ahmadmadyy/Coordinate-Tracking-Car/Hardware Design/1.png

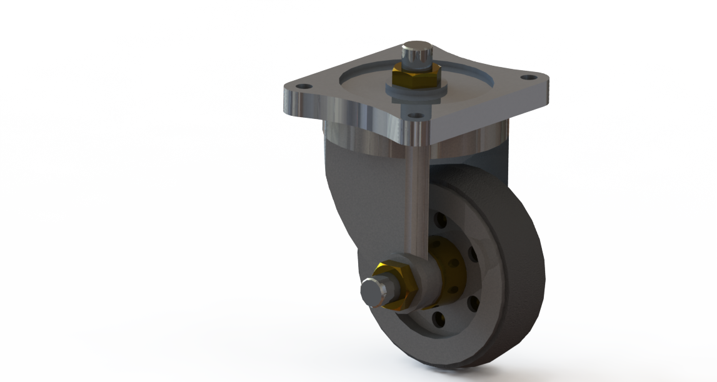
Hardware Design/1.png
