ahmadmadyy/Coordinate-Tracking-Car/Hardware Design/2021-05-19 (1).png

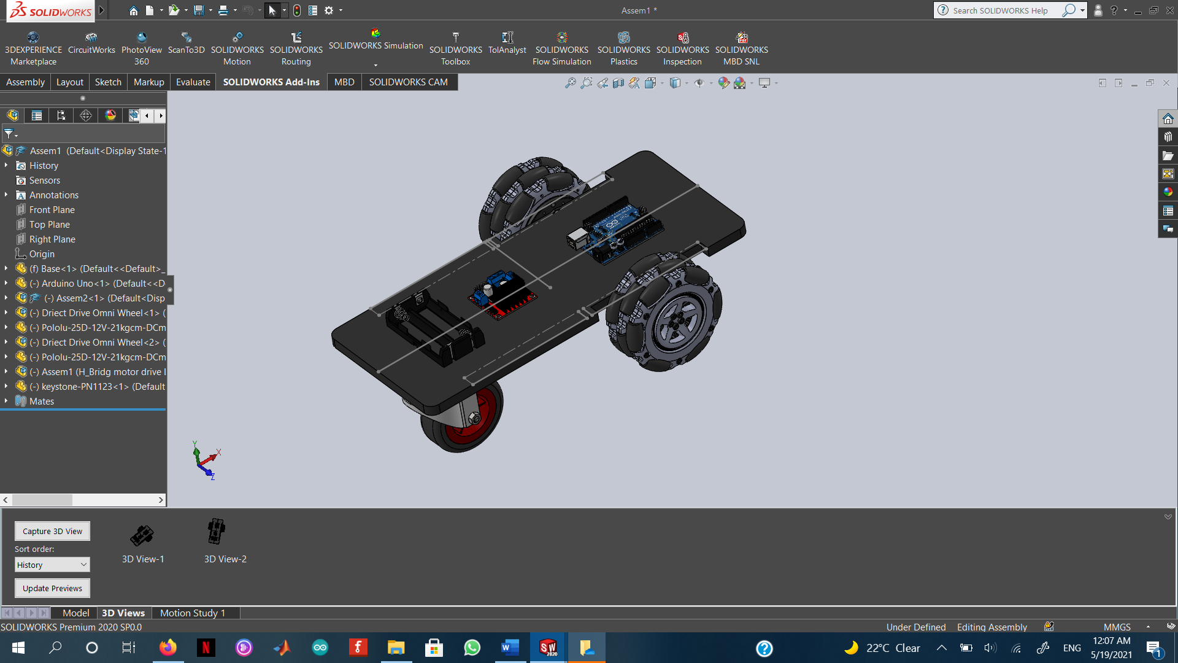
Hardware Design/2021-05-19 (1).png
