ahmadmadyy/Coordinate-Tracking-Car/Hardware Design/2021-05-19 (2).png

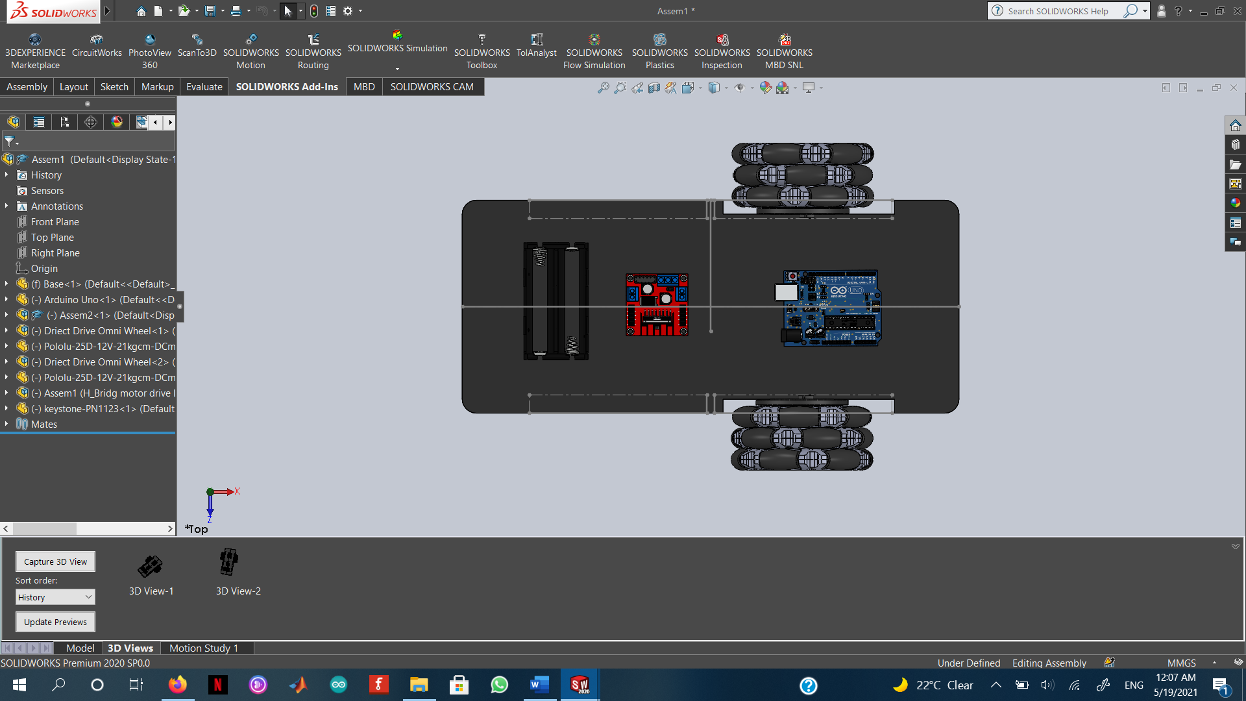
Hardware Design/2021-05-19 (2).png
