ahmadmadyy/Coordinate-Tracking-Car/Hardware Design/2021-05-19 (3).png

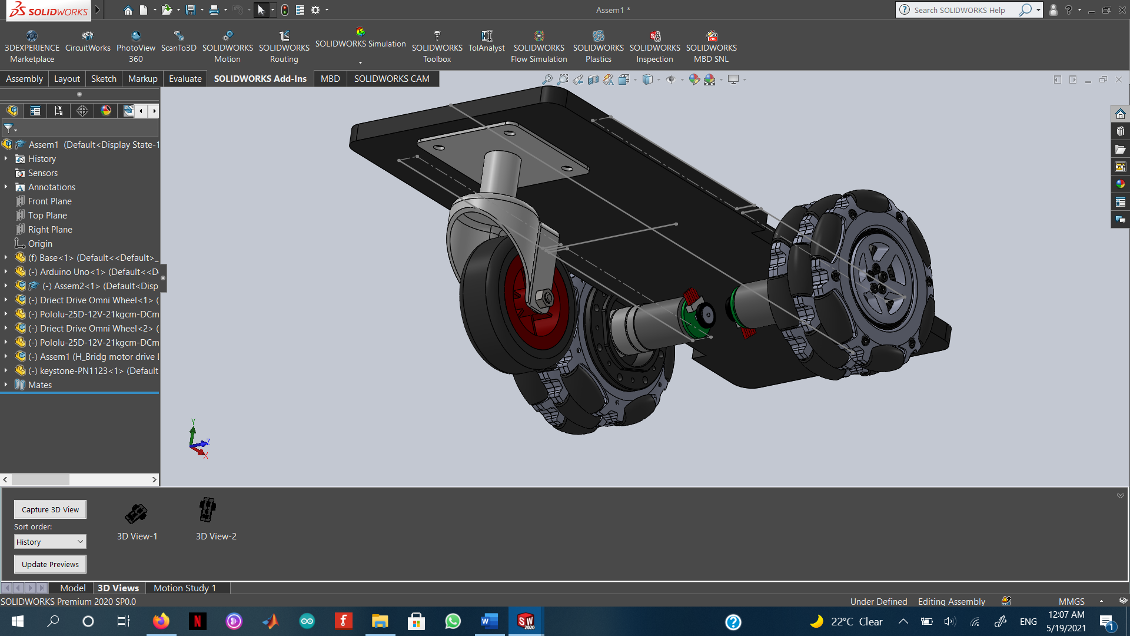
Hardware Design/2021-05-19 (3).png
