ahmadmadyy/Coordinate-Tracking-Car/Hardware Design/Capture2.PNG

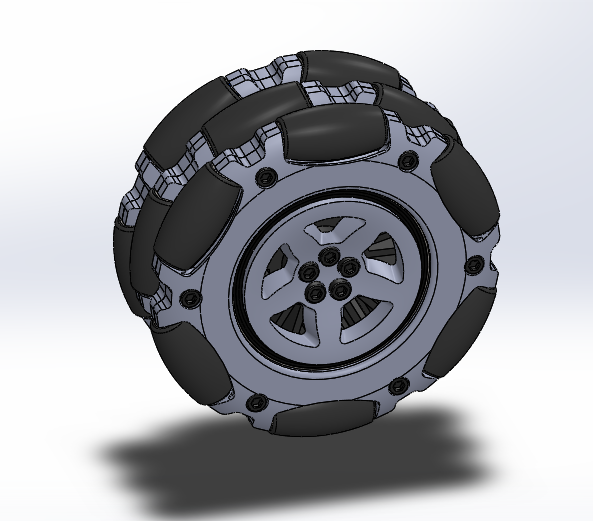
Hardware Design/Capture2.PNG
