ahmadmadyy/Coordinate-Tracking-Car/Hardware Design/Capture3.PNG

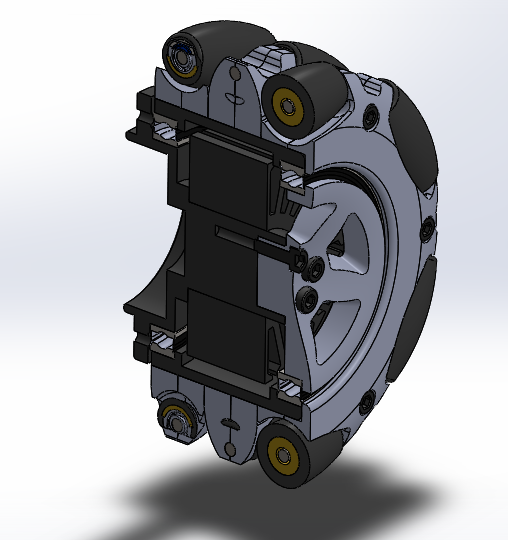
Hardware Design/Capture3.PNG
