ahmadmadyy/Coordinate-Tracking-Car/Hardware Design/Capture.JPG

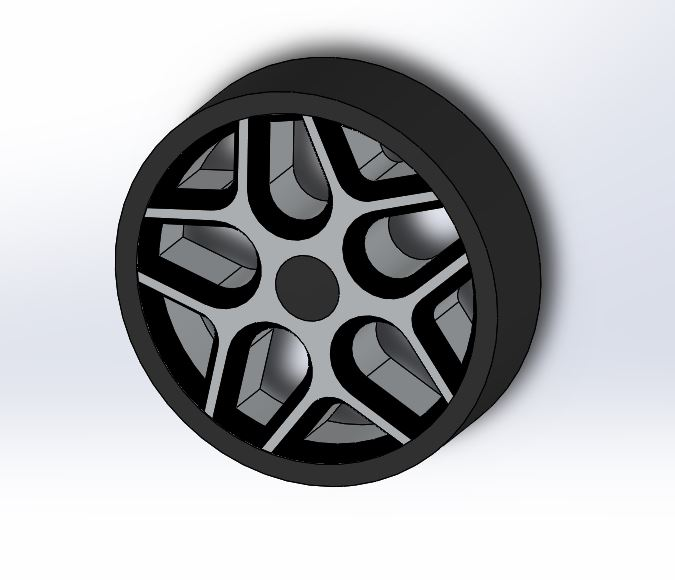
Hardware Design/Capture.JPG
