ahmadmadyy/Coordinate-Tracking-Car/Hardware Design/Capture.PNG

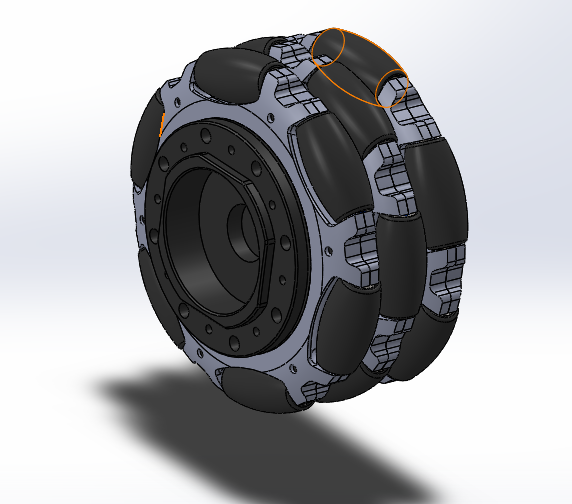
Hardware Design/Capture.PNG
