ahmadmadyy/Coordinate-Tracking-Car/Hardware Design/Castor wheel.JPG

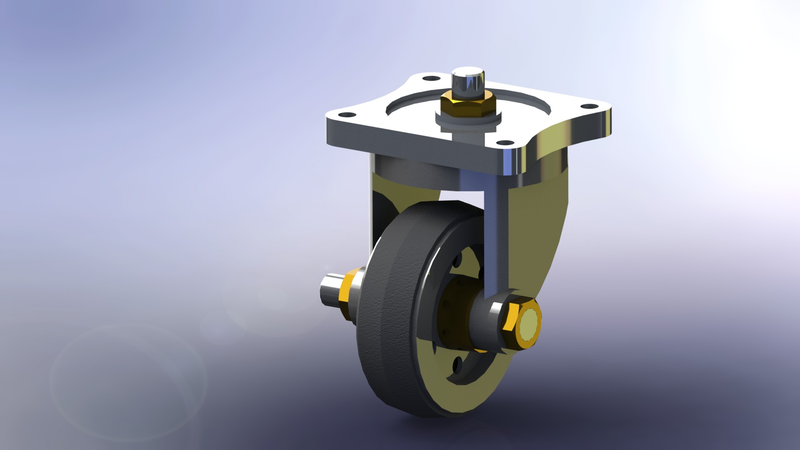
Hardware Design/Castor wheel.JPG
