ahmadmadyy/Coordinate-Tracking-Car/Hardware Design/h_bridg-motor-drive-l298n-1.snapshot.1/Assem final (H_Bridg)/Assem final (H_Bridg)/New folder/66.JPG

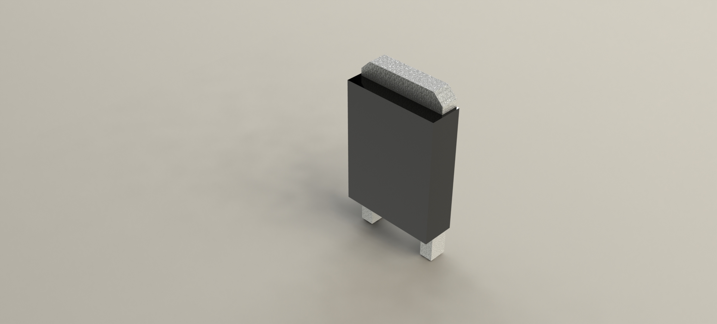
Hardware Design/h_bridg-motor-drive-l298n-1.snapshot.1/Assem final (H_Bridg)/Assem final (H_Bridg)/New folder/66.JPG
