ahmadmadyy/Coordinate-Tracking-Car/Hardware Design/keystone-PN1123 iso rendering 2.JPG

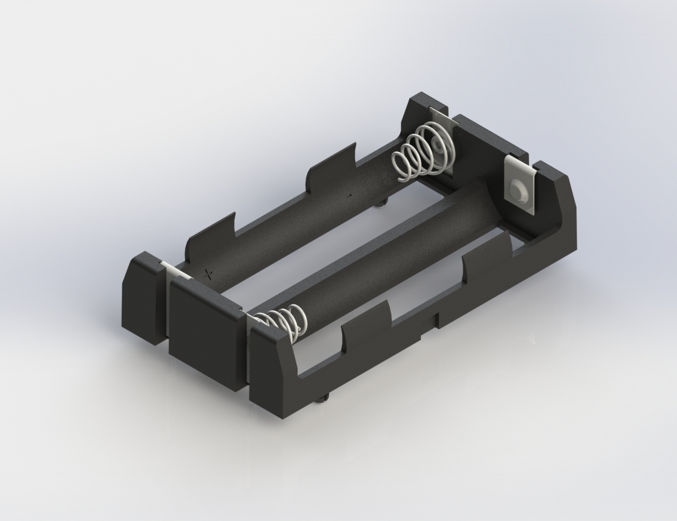
Hardware Design/keystone-PN1123 iso rendering 2.JPG
