ahmadmadyy/Coordinate-Tracking-Car/Hardware Design/keystone-PN1123 mechanical.JPG

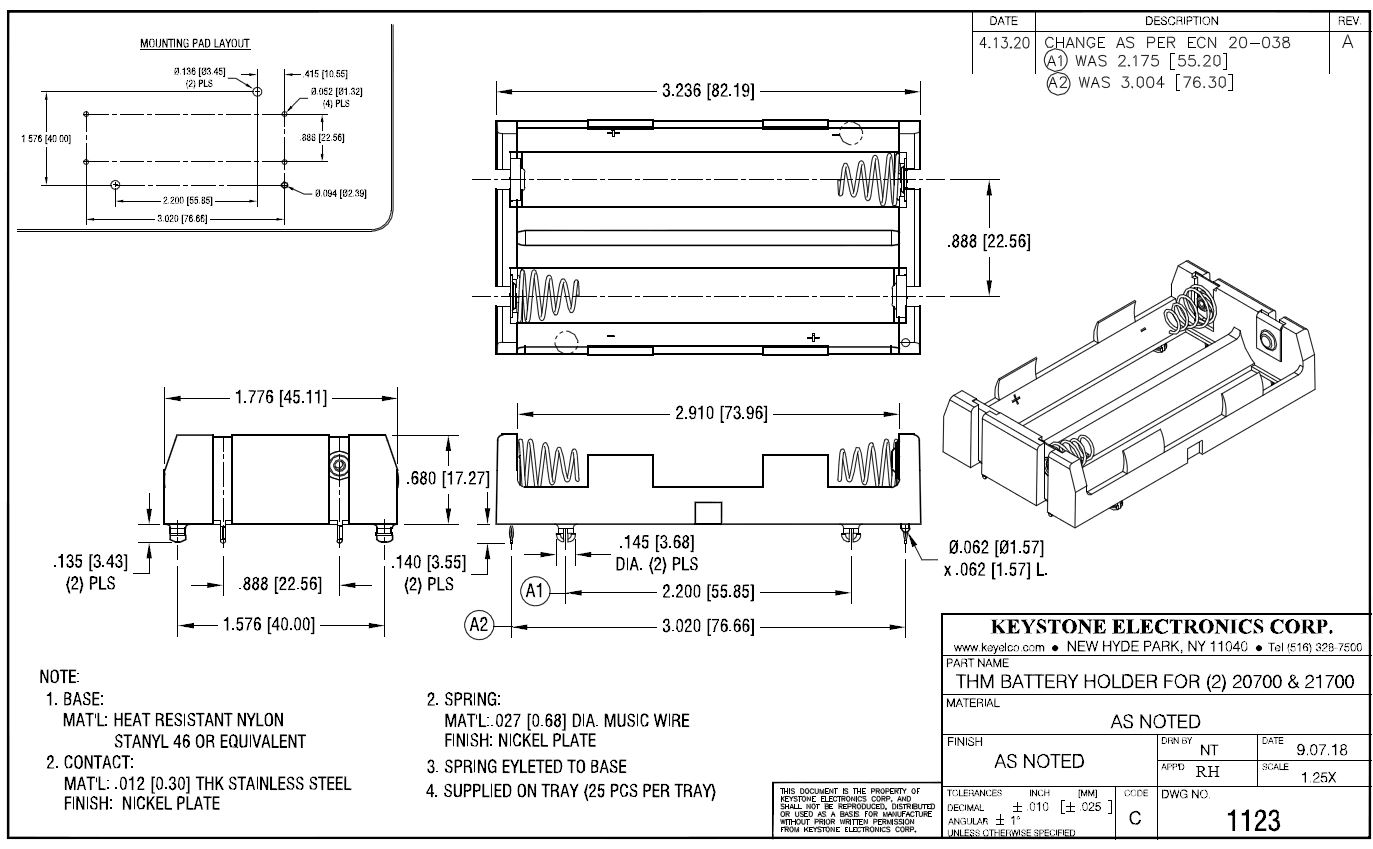
Hardware Design/keystone-PN1123 mechanical.JPG
