ahmadmadyy/Coordinate-Tracking-Car/Hardware Design/keystone-PN1123 photo.JPG

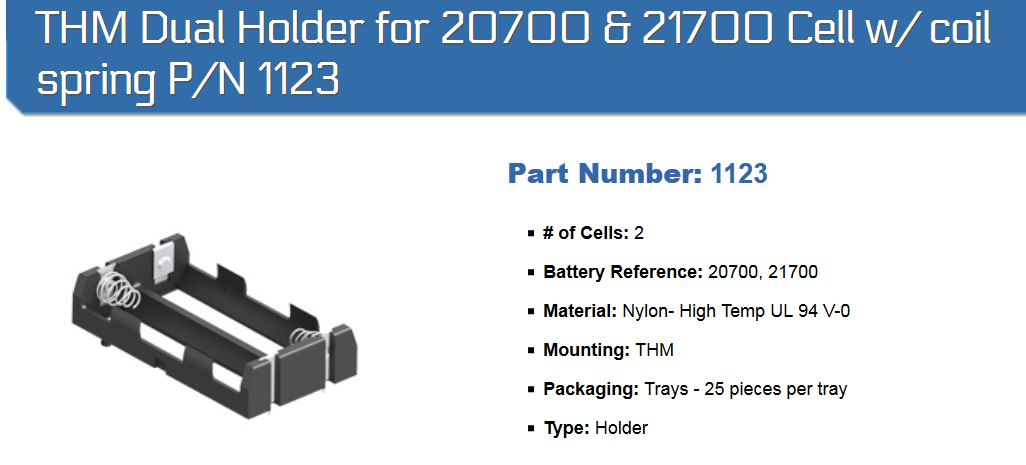
Hardware Design/keystone-PN1123 photo.JPG
