ahmadmadyy/Coordinate-Tracking-Car/Hardware Design/Renderings/untitled.642.jpg

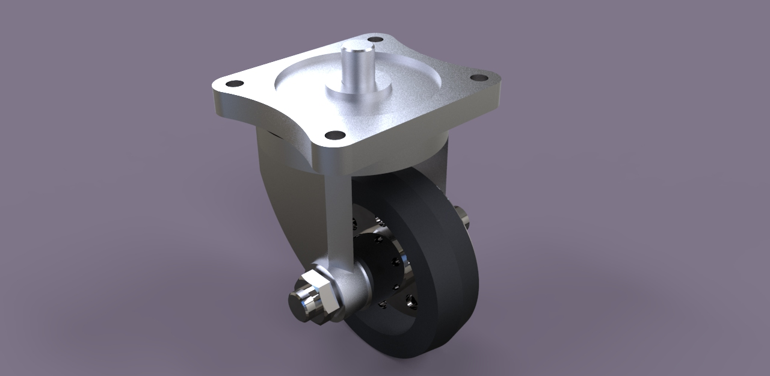
Hardware Design/Renderings/untitled.642.jpg
