ahmadmadyy/Coordinate-Tracking-Car/Hardware Design/View.JPG

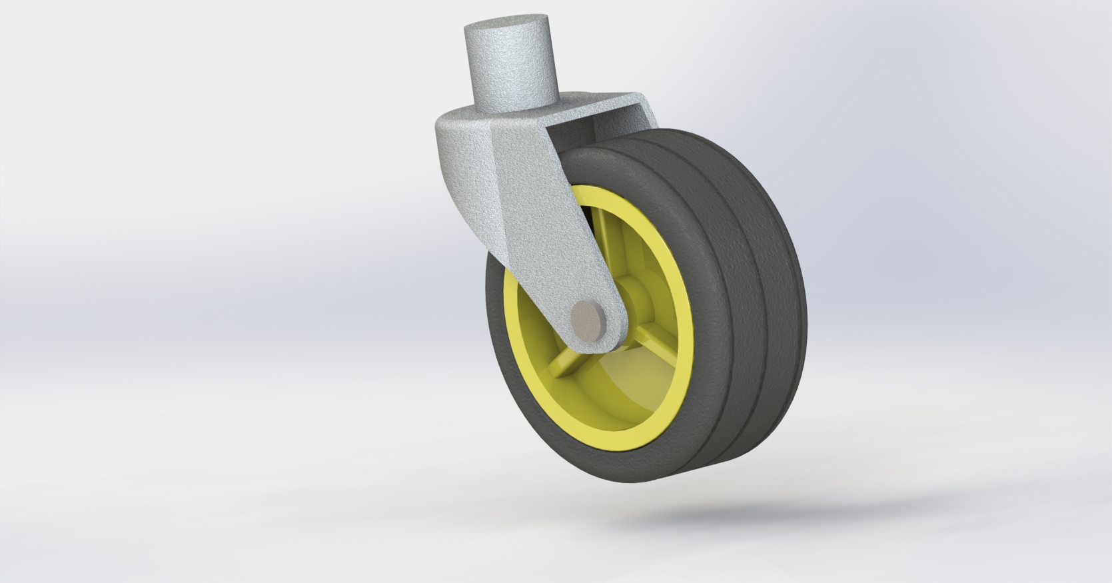
Hardware Design/View.JPG
