ahmadmadyy/Coordinate-Tracking-Car/Hardware Design/wheel/JPG/Assem2.JPG

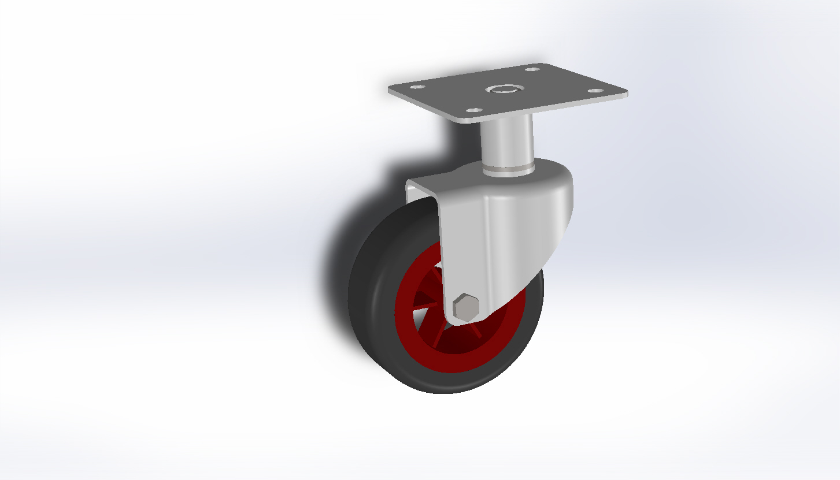
Hardware Design/wheel/JPG/Assem2.JPG
