ahmadmadyy/Coordinate-Tracking-Car/Hardware Design/wheel/JPG/Assem3.JPG

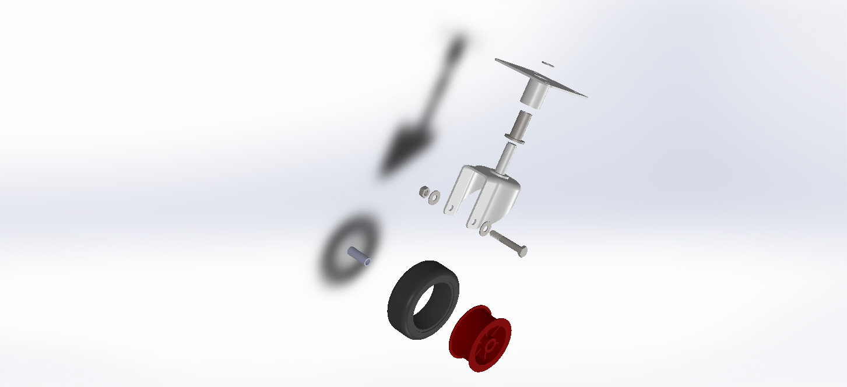
Hardware Design/wheel/JPG/Assem3.JPG
