ahmadmadyy/Coordinate-Tracking-Car/Hardware Design/wheel/JPG/Ring.JPG

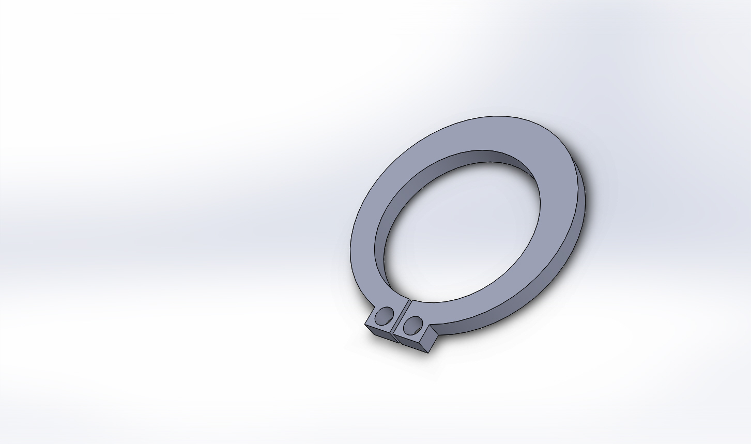
Hardware Design/wheel/JPG/Ring.JPG
