ahmadmadyy/Coordinate-Tracking-Car/Hardware Design/wheel/JPG/screw M6.JPG

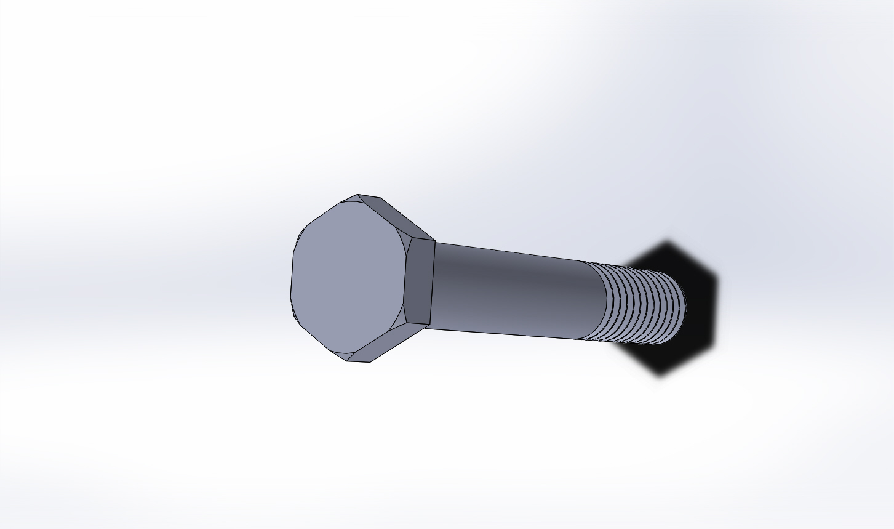
Hardware Design/wheel/JPG/screw M6.JPG
