ahmadmadyy/Coordinate-Tracking-Car/Hardware Design/wheel/JPG/screw nut m6.JPG

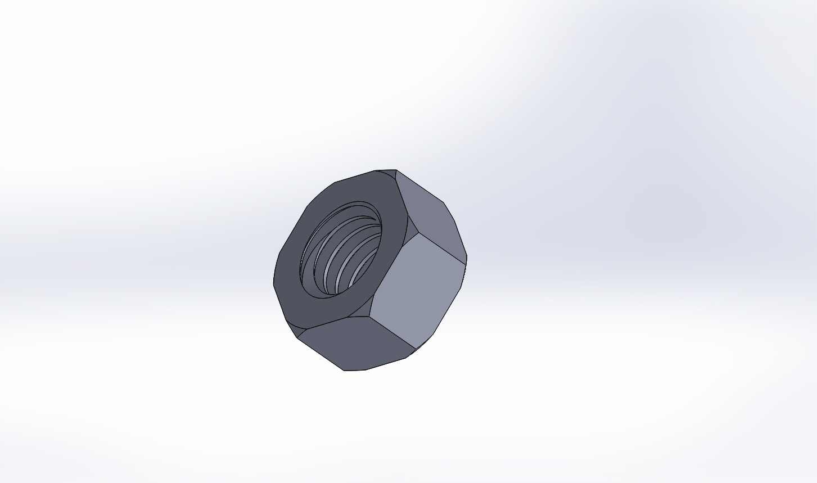
Hardware Design/wheel/JPG/screw nut m6.JPG
