ahmadmadyy/Coordinate-Tracking-Car/Hardware Design/wheel/JPG/Support plate .JPG

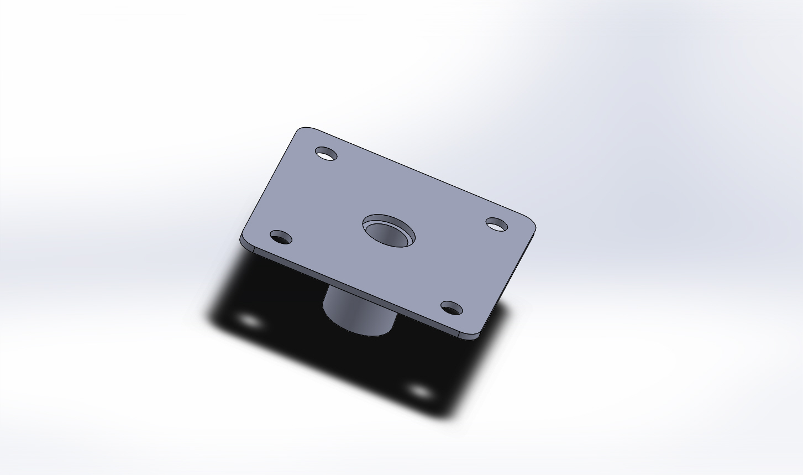
Hardware Design/wheel/JPG/Support plate .JPG
