ahmadmadyy/Coordinate-Tracking-Car/Hardware Design/wheel/JPG/tire.JPG

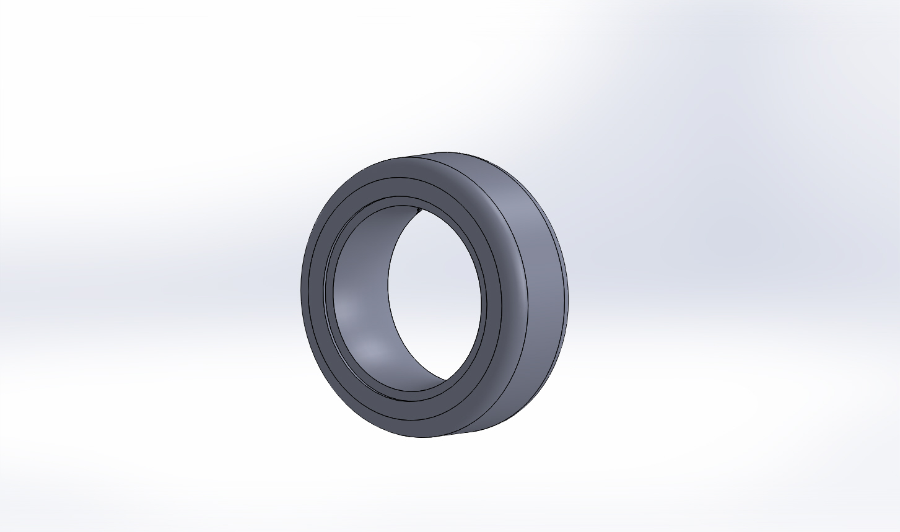
Hardware Design/wheel/JPG/tire.JPG
