ahmadmadyy/Coordinate-Tracking-Car/Hardware Design/wheel/JPG/wheel carrier.JPG

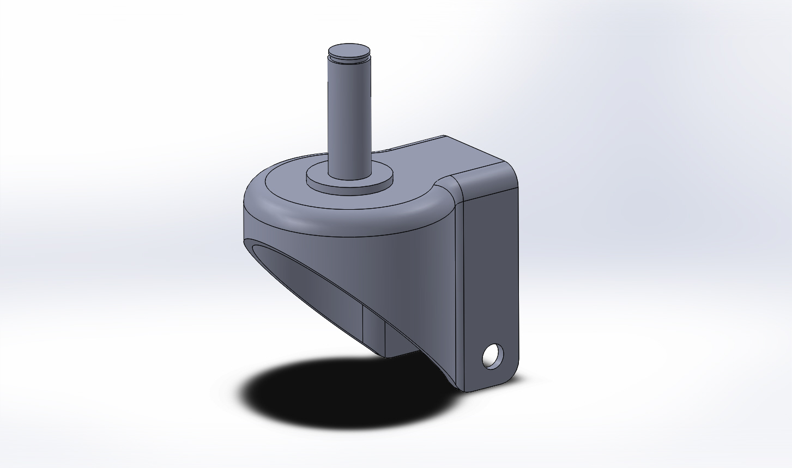
Hardware Design/wheel/JPG/wheel carrier.JPG
