ahmadmadyy/Coordinate-Tracking-Car/Hardware Design/wheel/JPG/wheel.JPG

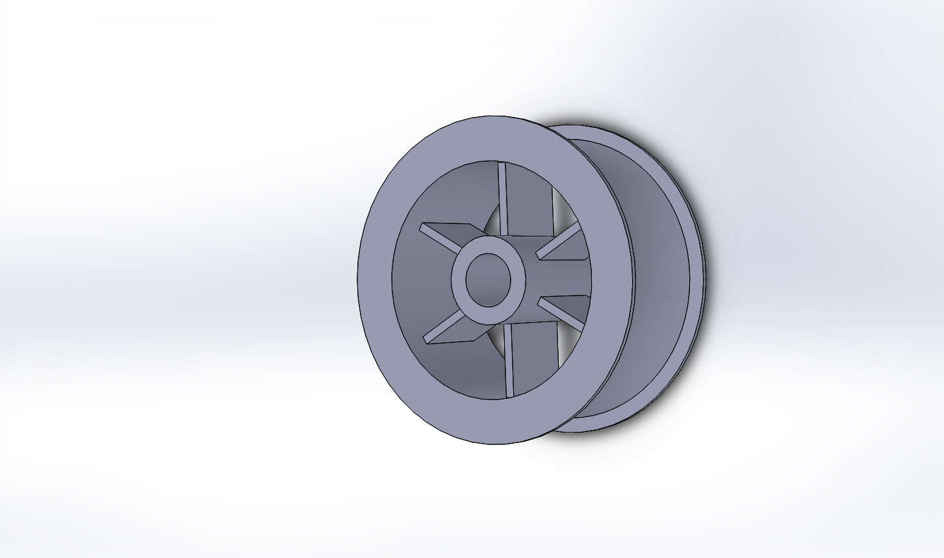
Hardware Design/wheel/JPG/wheel.JPG
