ahmadmadyy/Coordinate-Tracking-Car/Hardware Design/Поворотные колесо d200мм/render_1.jpg

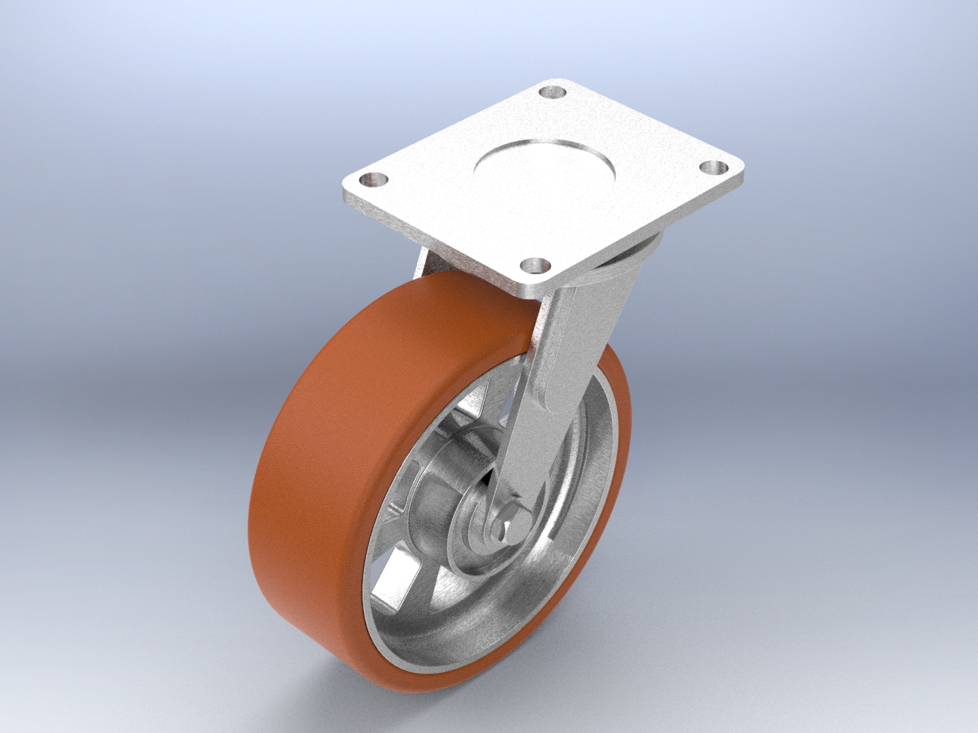
Hardware Design/Поворотные колесо d200мм/render_1.jpg
