ahmadmadyy/Coordinate-Tracking-Car/Hardware Design/Поворотные колесо d200мм/render_2.jpg

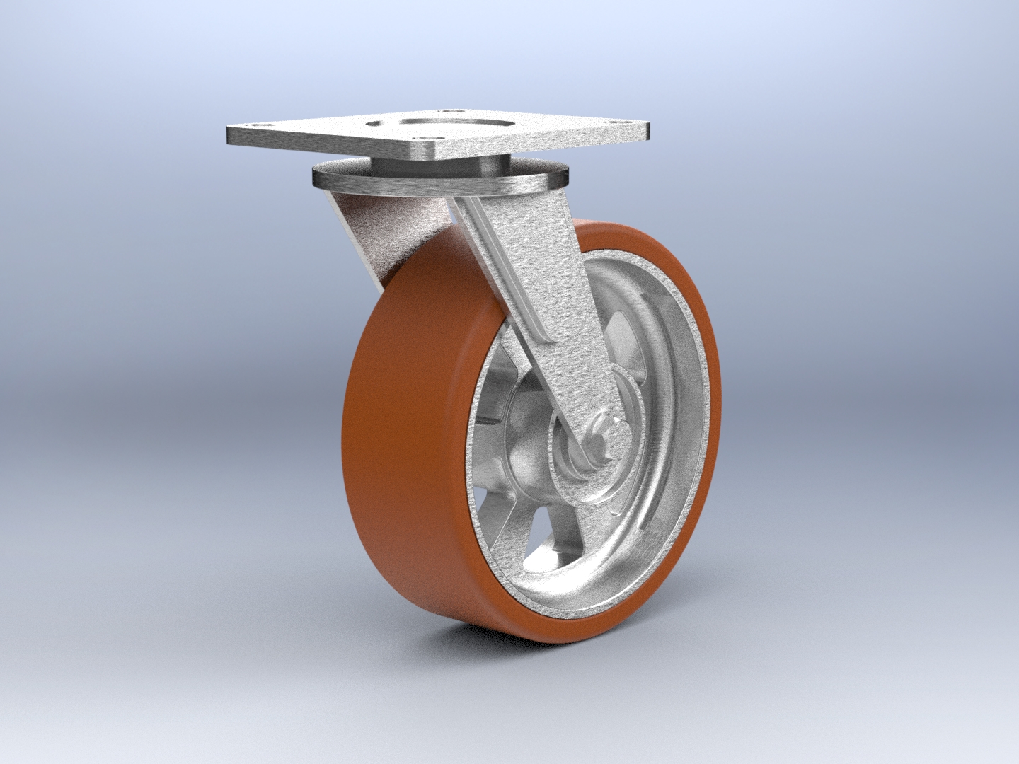
Hardware Design/Поворотные колесо d200мм/render_2.jpg
