ahmadmadyy/Coordinate-Tracking-Car/Hardware Design/Поворотные колесо d200мм/render_3.jpg

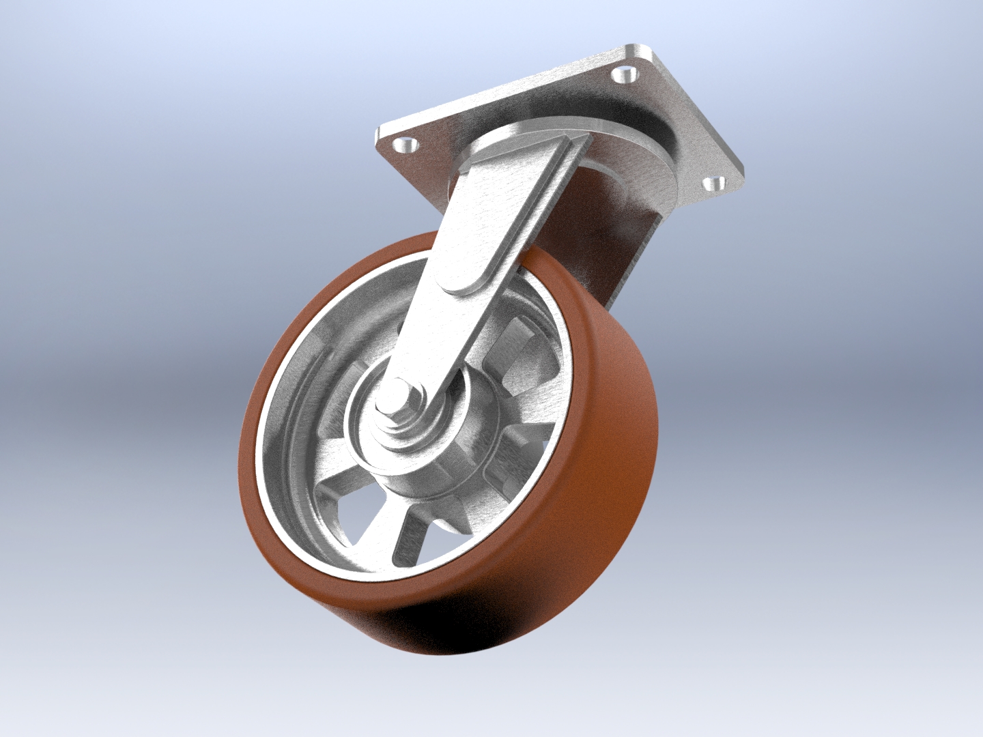
Hardware Design/Поворотные колесо d200мм/render_3.jpg
