ahmadmadyy/Coordinate-Tracking-Car/Media/20210617_170247.jpg

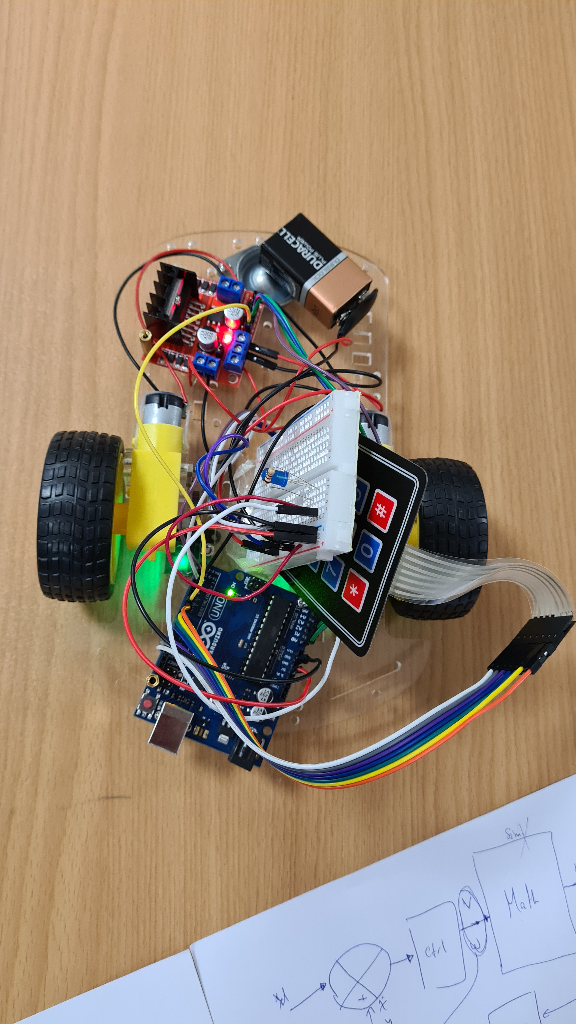
Media/20210617_170247.jpg
