ahmadmadyy/Coordinate-Tracking-Car/Media/20210617_170249.jpg

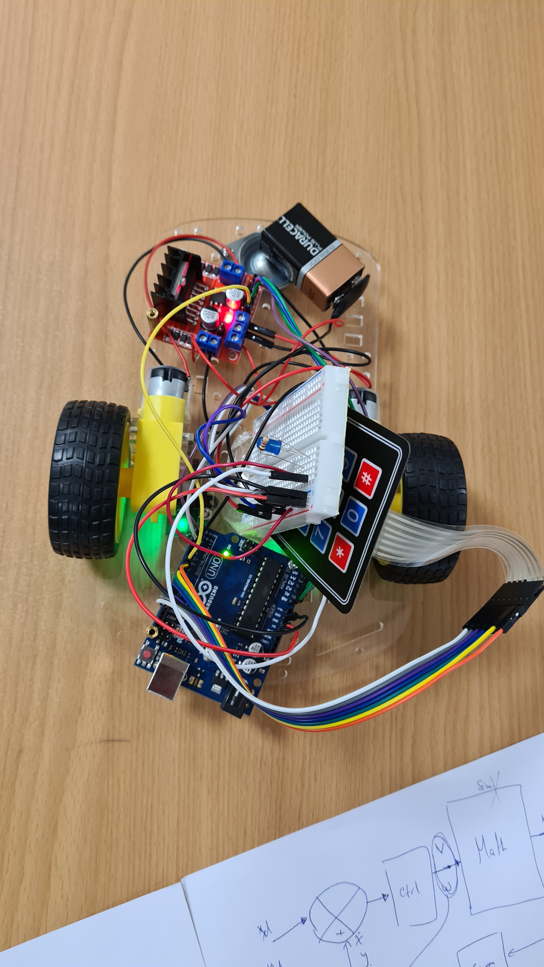
Media/20210617_170249.jpg
