ahmadmadyy/Coordinate-Tracking-Car/Media/20210622_192925.jpg

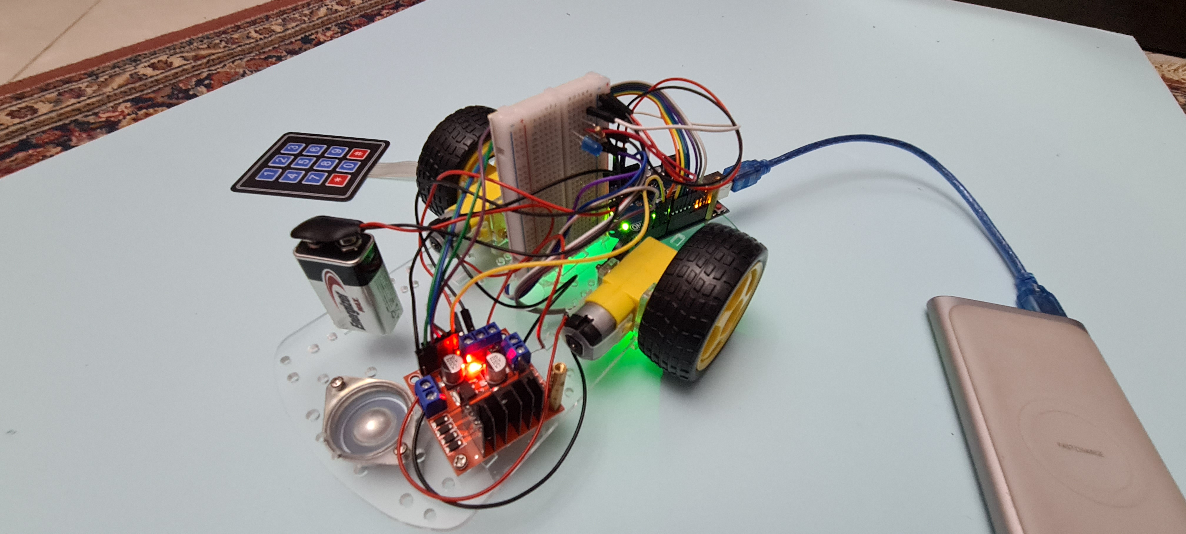
Media/20210622_192925.jpg
