ahmadmadyy/Coordinate-Tracking-Car/Media/20210622_192959.jpg

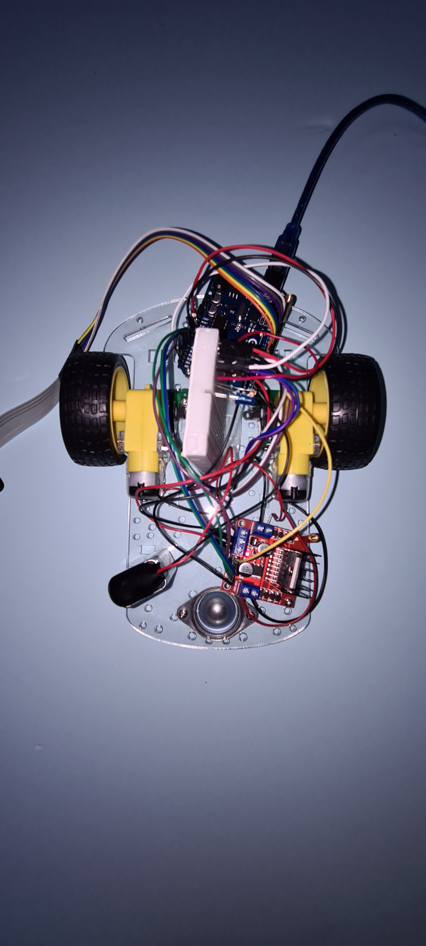
Media/20210622_192959.jpg
