ahmadmadyy/Coordinate-Tracking-Car/Media/20210622_193133.jpg

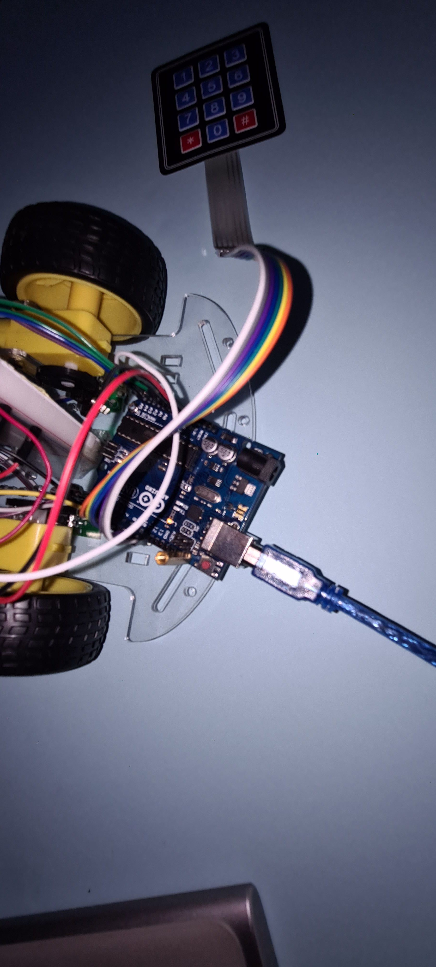
Media/20210622_193133.jpg
