ahmadmadyy/Coordinate-Tracking-Car/Media/20210622_193256.jpg

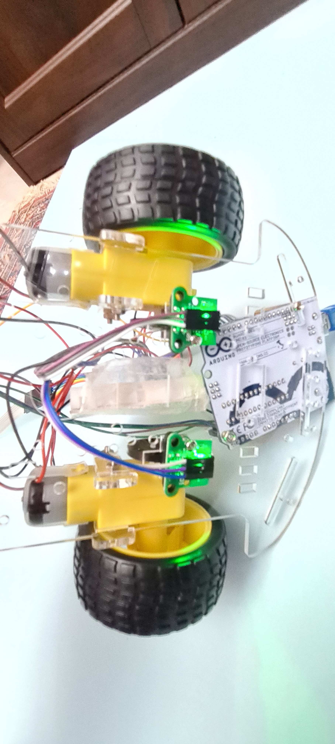
Media/20210622_193256.jpg
