ahmadmadyy/Coordinate-Tracking-Car/Media/20210622_193330.jpg

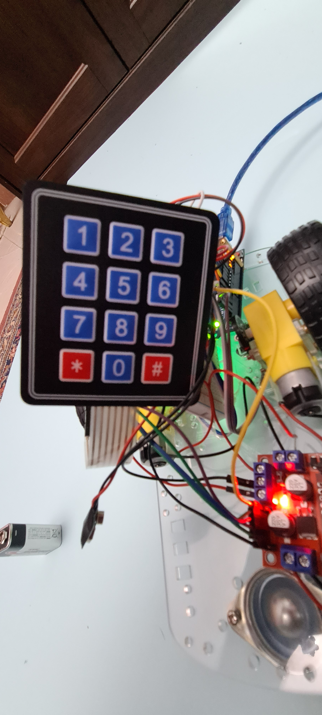
Media/20210622_193330.jpg
