ahmadmadyy/Coordinate-Tracking-Car/Hardware Design/h_bridg-motor-drive-l298n-1.snapshot.1/Assem final (H_Bridg)/Dual pin header.SLDPRT

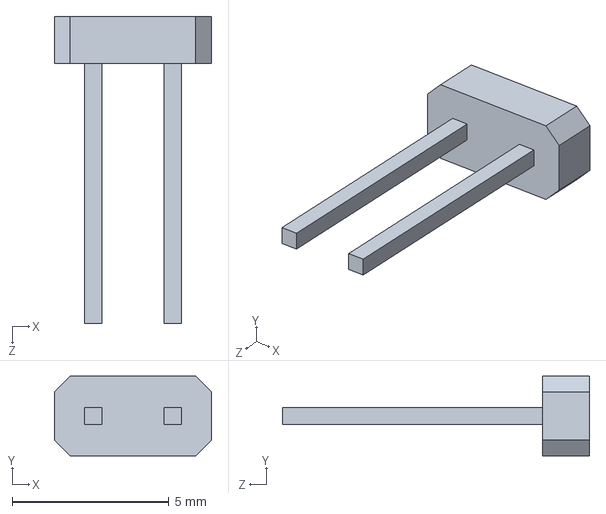
[picture p91: CAD file, 2023-09-04]
Hardware Design/h_bridg-motor-drive-l298n-1.snapshot.1/Assem final (H_Bridg)/Dual pin header.SLDPRT
5.00 x 2.54 x 9.80 mm
