ahmadmadyy/Coordinate-Tracking-Car/Hardware Design/wheel/Support plate .SLDPRT

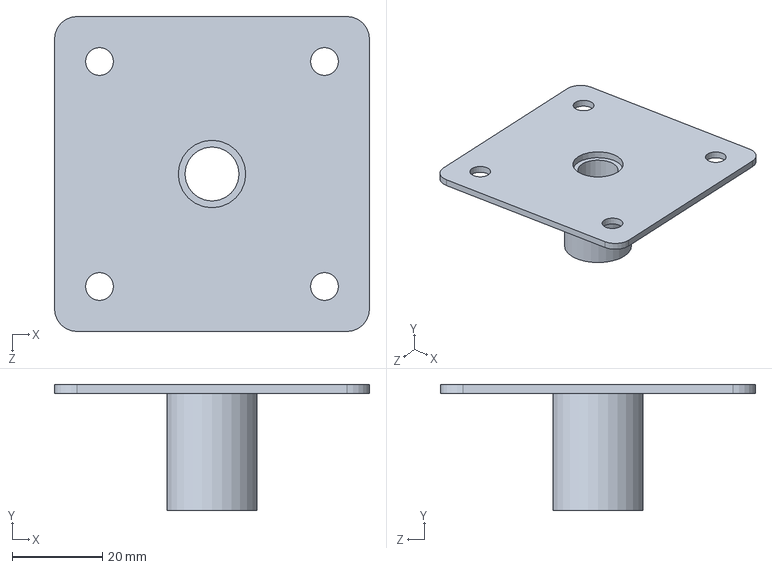
[picture p92: CAD file, 2023-09-04]
Hardware Design/wheel/Support plate .SLDPRT
70.0 x 28.0 x 70.0 mm
