ahmadmadyy/Coordinate-Tracking-Car/Hardware Design/h_bridg-motor-drive-l298n-1.snapshot.1/Assem final (H_Bridg)/Diode.SLDPRT

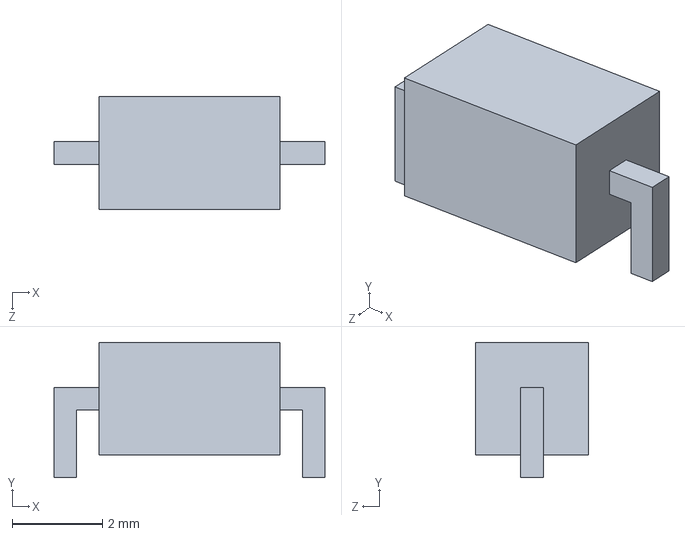
[picture p93: CAD file, 2023-09-04]
Hardware Design/h_bridg-motor-drive-l298n-1.snapshot.1/Assem final (H_Bridg)/Diode.SLDPRT
6.00 x 3.00 x 2.50 mm
