ahmadmadyy/Coordinate-Tracking-Car/Hardware Design/Pololu-25D-12V-21kgcm-DCmotor.SLDPRT

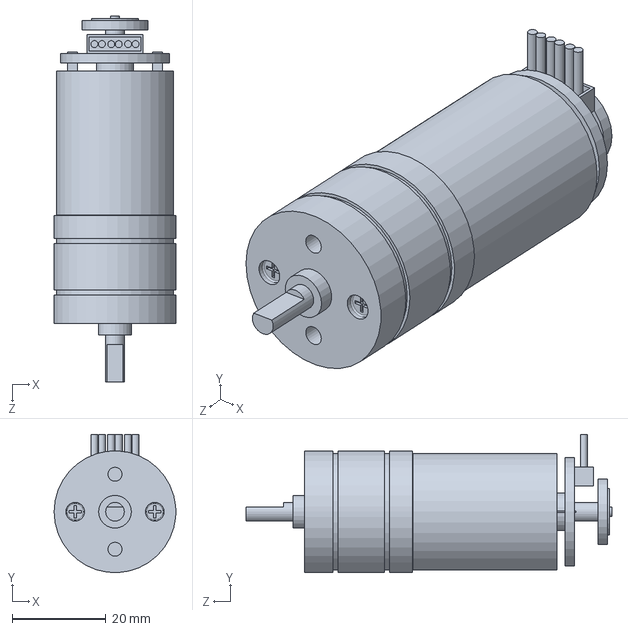
[picture p94: CAD file, 2023-09-04]
Hardware Design/Pololu-25D-12V-21kgcm-DCmotor.SLDPRT
26.0 x 29.5 x 78.1 mm
