ahmadmadyy/Coordinate-Tracking-Car/Hardware Design/DDM Cap.SLDPRT

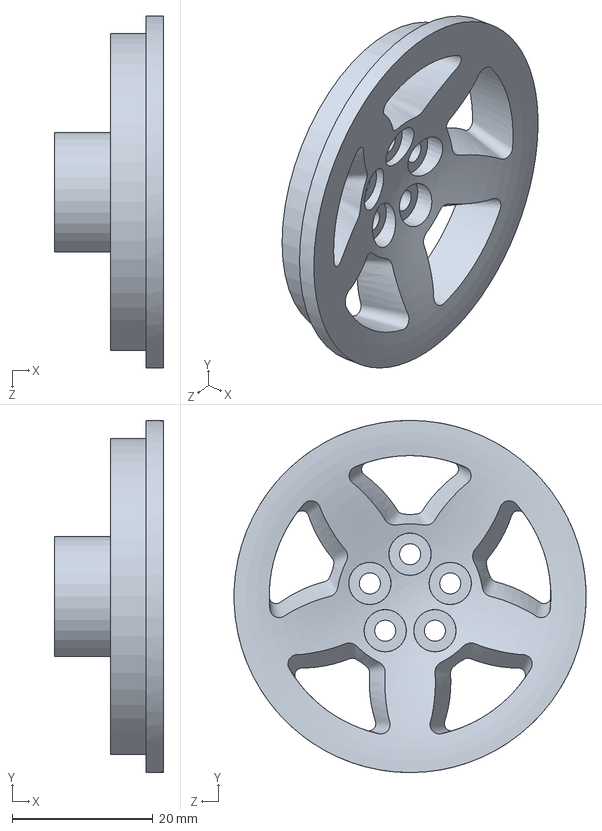
[picture p95: CAD file, 2023-09-04]
Hardware Design/DDM Cap.SLDPRT
15.5 x 50.0 x 50.0 mm
