ahmadmadyy/Coordinate-Tracking-Car/Hardware Design/h_bridg-motor-drive-l298n-1.snapshot.1/Assem final (H_Bridg)/Pin header.SLDPRT

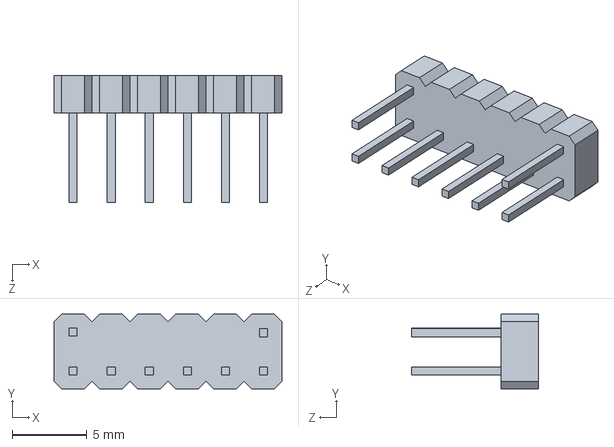
[picture p96: CAD file, 2023-09-04]
Hardware Design/h_bridg-motor-drive-l298n-1.snapshot.1/Assem final (H_Bridg)/Pin header.SLDPRT
15.3 x 5.00 x 8.50 mm
