ahmadmadyy/Coordinate-Tracking-Car/Hardware Design/DDm Stator laminet.SLDPRT

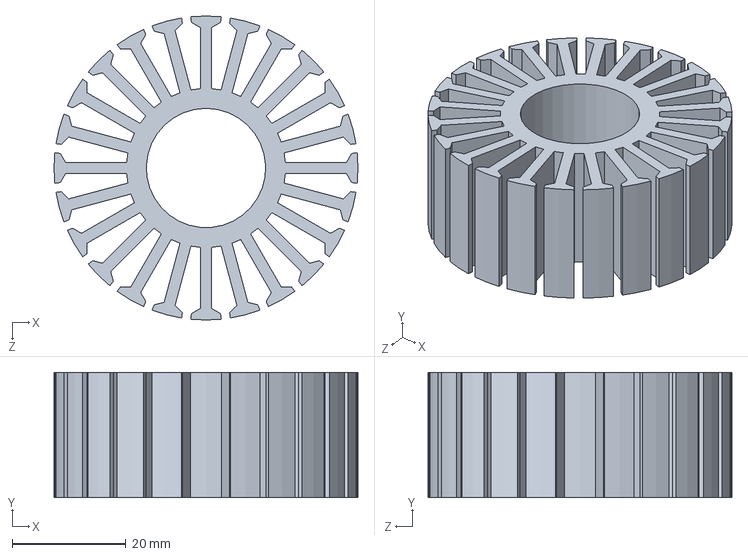
[picture p97: CAD file, 2023-09-04]
Hardware Design/DDm Stator laminet.SLDPRT
53.5 x 22.0 x 53.5 mm
