ahmadmadyy/Coordinate-Tracking-Car/Hardware Design/wheel/bearing .SLDPRT

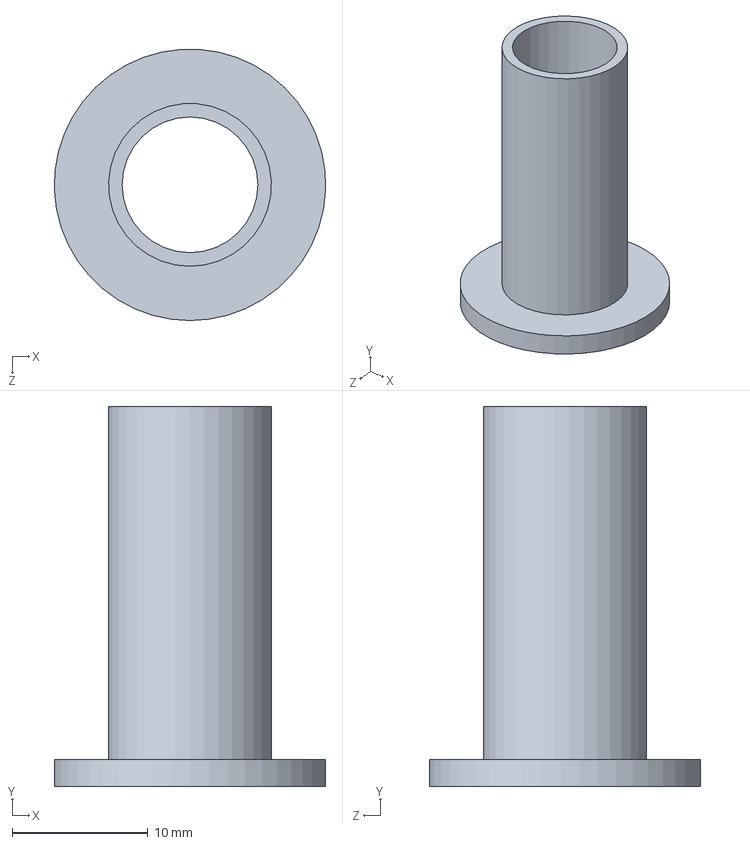
[picture p98: CAD file, 2023-09-04]
Hardware Design/wheel/bearing .SLDPRT
20.0 x 28.0 x 20.0 mm
