ahmadmadyy/Coordinate-Tracking-Car/Hardware Design/h_bridg-motor-drive-l298n-1.snapshot.1/Assem final (H_Bridg)/Capacitor.SLDPRT

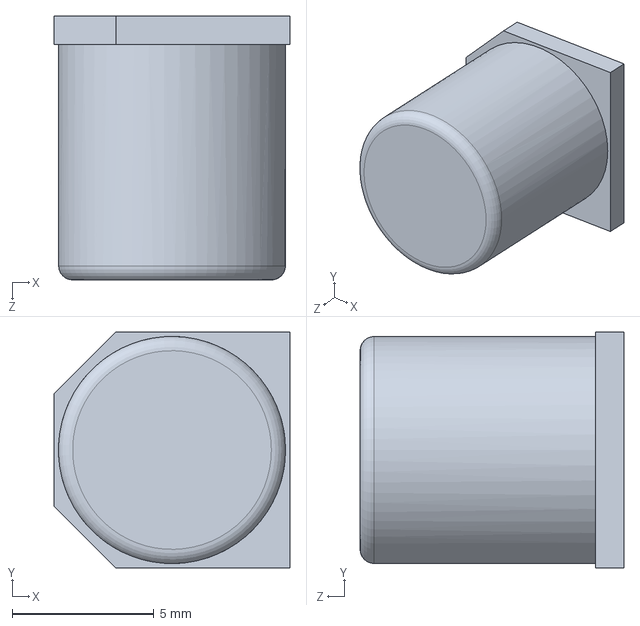
[picture p99: CAD file, 2023-09-04]
Hardware Design/h_bridg-motor-drive-l298n-1.snapshot.1/Assem final (H_Bridg)/Capacitor.SLDPRT
8.30 x 8.30 x 9.30 mm
