ahmadmadyy/Coordinate-Tracking-Car/Hardware Design/keystone-PN1123.SLDPRT

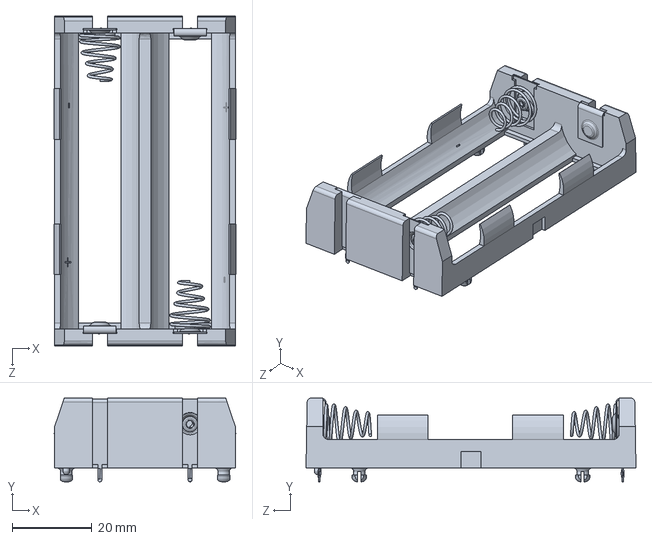
[picture p100: CAD file, 2023-09-04]
Hardware Design/keystone-PN1123.SLDPRT
45.4 x 21.0 x 82.6 mm
