ahmadmadyy/Coordinate-Tracking-Car/Hardware Design/Cross shaft D.SLDPRT

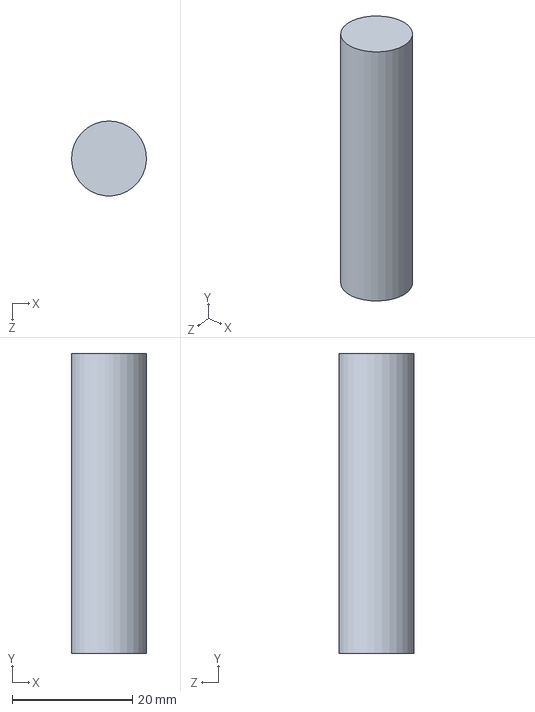
[picture p101: CAD file, 2023-09-04]
Hardware Design/Cross shaft D.SLDPRT
12.5 x 50.0 x 12.5 mm
