ahmadmadyy/Coordinate-Tracking-Car/Hardware Design/h_bridg-motor-drive-l298n-1.snapshot.1/Assem final (H_Bridg)/L298N.SLDPRT

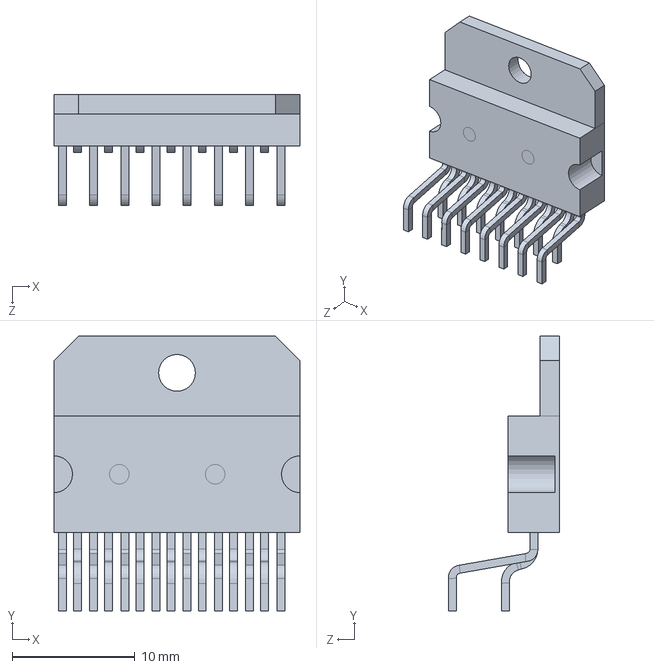
[picture p102: CAD file, 2023-09-04]
Hardware Design/h_bridg-motor-drive-l298n-1.snapshot.1/Assem final (H_Bridg)/L298N.SLDPRT
20.0 x 22.4 x 9.07 mm
