ahmadmadyy/Coordinate-Tracking-Car/Hardware Design/wheel/wheel carrier.SLDPRT

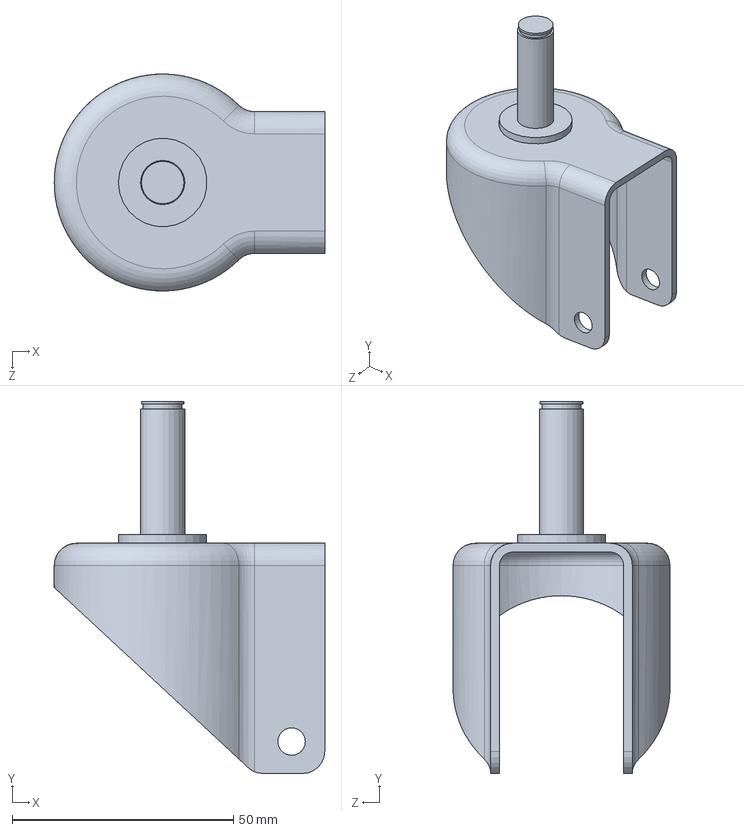
[picture p103: CAD file, 2023-09-04]
Hardware Design/wheel/wheel carrier.SLDPRT
61.1 x 84.0 x 49.0 mm
