ahmadmadyy/Coordinate-Tracking-Car/Hardware Design/wheel/tire.SLDPRT

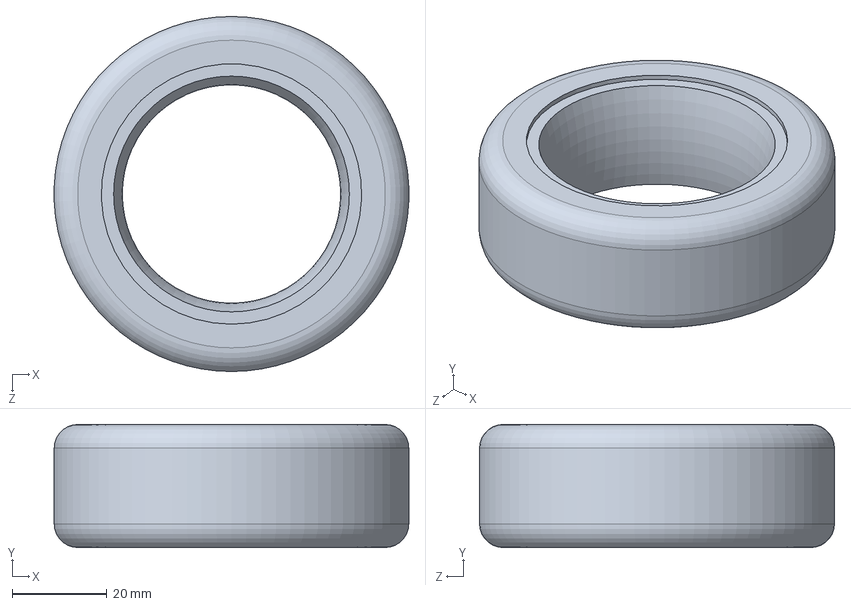
[picture p104: CAD file, 2023-09-04]
Hardware Design/wheel/tire.SLDPRT
74.9 x 26.0 x 75.0 mm
