ahmadmadyy/Coordinate-Tracking-Car/Hardware Design/DDOW Roller Shaft.SLDPRT

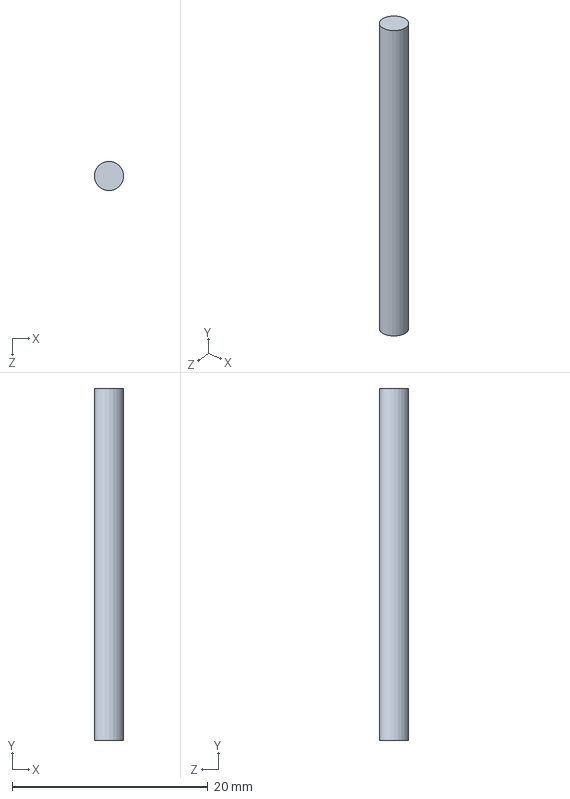
[picture p105: CAD file, 2023-09-04]
Hardware Design/DDOW Roller Shaft.SLDPRT
3.00 x 36.0 x 3.00 mm
