ahmadmadyy/Coordinate-Tracking-Car/Hardware Design/wheel/pipe.SLDPRT

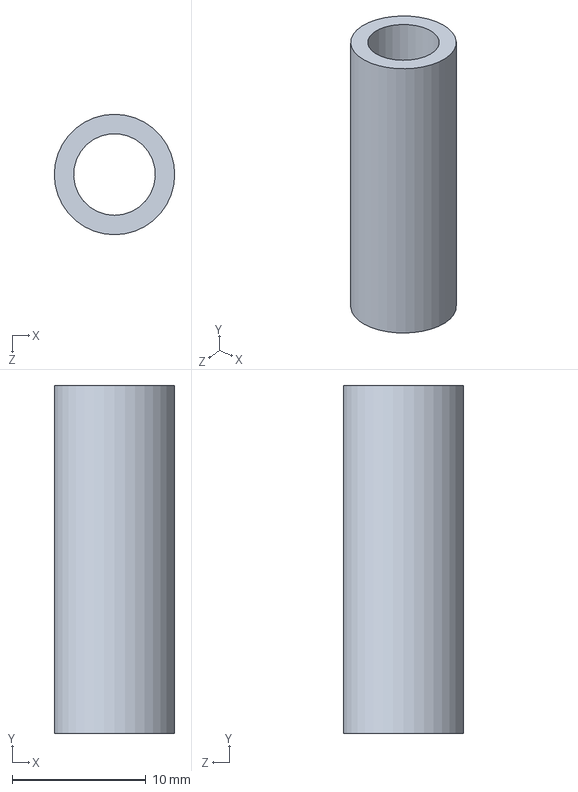
[picture p107: CAD file, 2023-09-04]
Hardware Design/wheel/pipe.SLDPRT
9.00 x 26.0 x 9.00 mm
