ahmadmadyy/Coordinate-Tracking-Car/Hardware Design/W 638_3 R-2RS1.SLDPRT

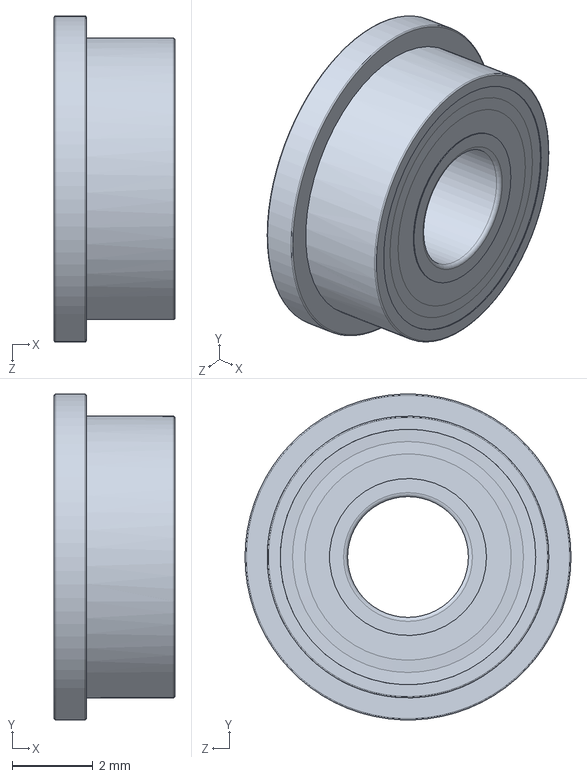
[picture p108: CAD file, 2023-09-04]
Hardware Design/W 638_3 R-2RS1.SLDPRT
3.00 x 8.09 x 8.10 mm
