ahmadmadyy/Coordinate-Tracking-Car/Hardware Design/Base.SLDPRT

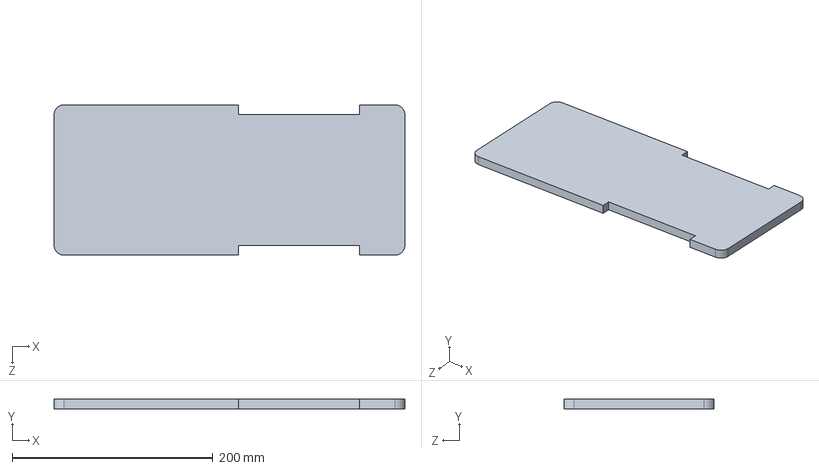
[picture p109: CAD file, 2023-09-04]
Hardware Design/Base.SLDPRT
350.0 x 10.0 x 150.0 mm
