ahmadmadyy/Coordinate-Tracking-Car/Hardware Design/DDM Bace.SLDPRT

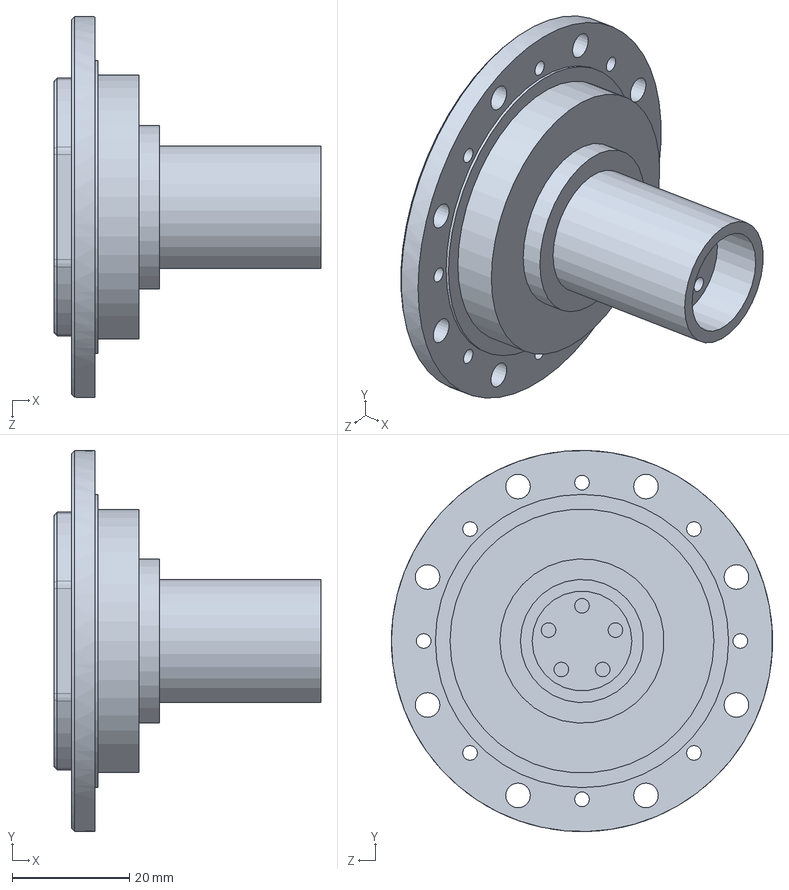
[picture p110: CAD file, 2023-09-04]
Hardware Design/DDM Bace.SLDPRT
45.5 x 65.0 x 65.0 mm
