ahmadmadyy/Coordinate-Tracking-Car/Hardware Design/DriveWheel-PunctureProof220.SLDPRT

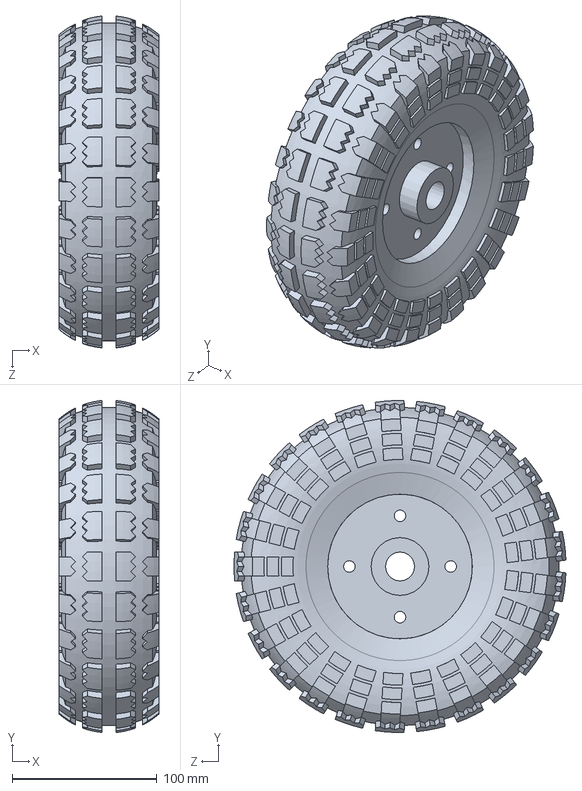
[picture p111: CAD file, 2023-09-04]
Hardware Design/DriveWheel-PunctureProof220.SLDPRT
69.0 x 229.5 x 229.4 mm
