ahmadmadyy/Coordinate-Tracking-Car/Hardware Design/Base tire.SLDPRT

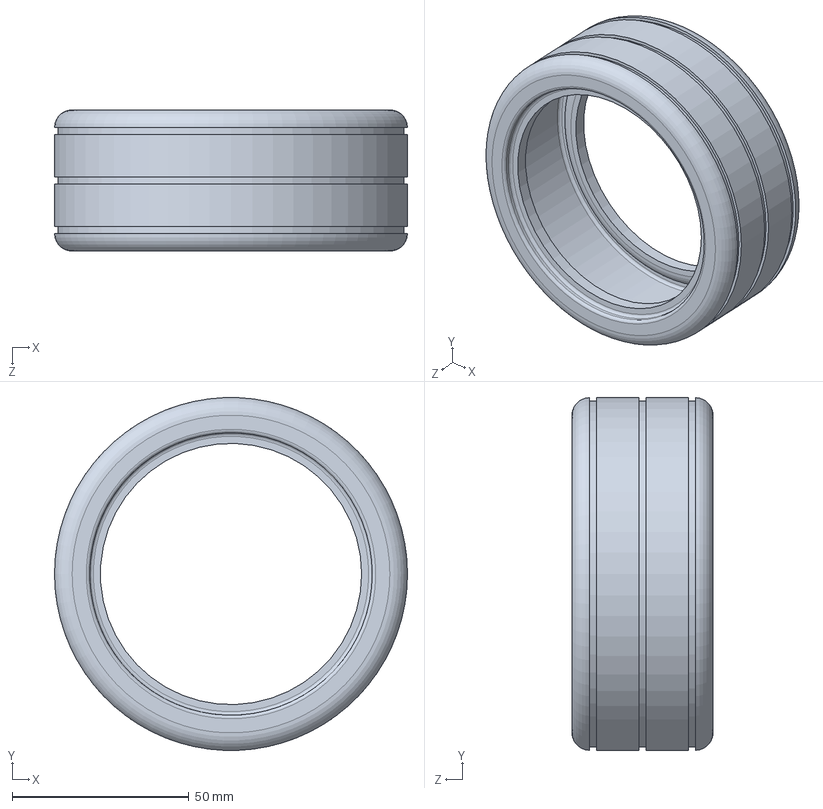
[picture p112: CAD file, 2023-09-04]
Hardware Design/Base tire.SLDPRT
100.0 x 100.0 x 40.0 mm
