ahmadmadyy/Coordinate-Tracking-Car/Hardware Design/Wheel D65x25.SLDPRT

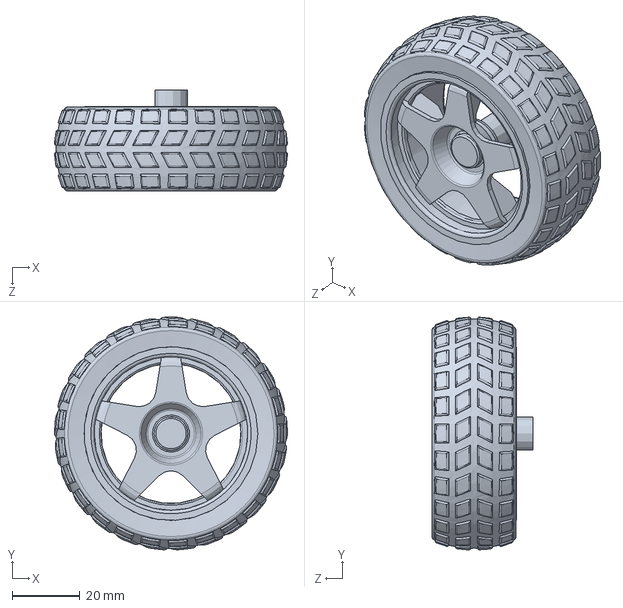
[picture p113: CAD file, 2023-09-04]
Hardware Design/Wheel D65x25.SLDPRT
68.9 x 68.8 x 30.0 mm
