ahmadmadyy/Coordinate-Tracking-Car/Hardware Design/DDOW Part 3.SLDPRT

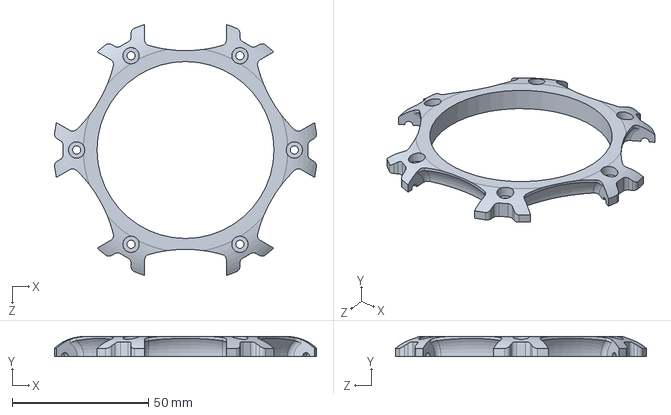
[picture p114: CAD file, 2023-09-04]
Hardware Design/DDOW Part 3.SLDPRT
96.3 x 7.50 x 92.2 mm
