ahmadmadyy/Coordinate-Tracking-Car/Hardware Design/Car Wheel.SLDPRT

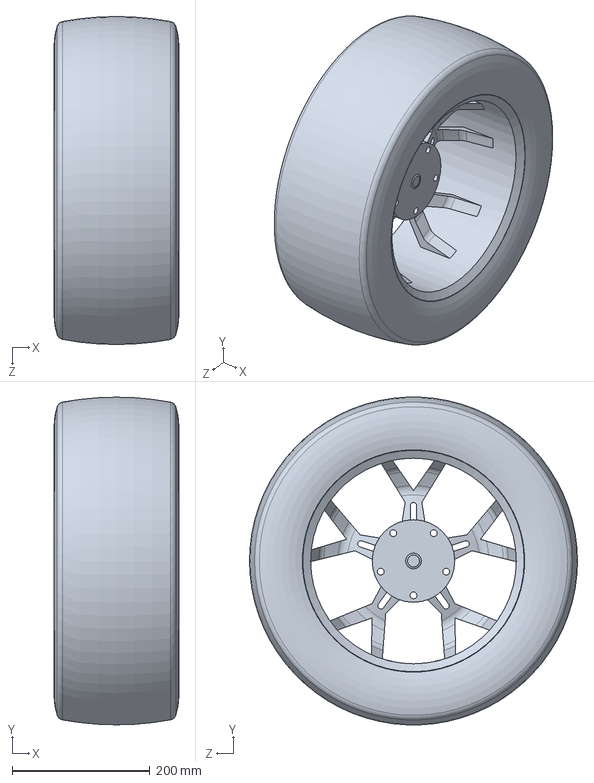
[picture p115: CAD file, 2023-09-04]
Hardware Design/Car Wheel.SLDPRT
181.3 x 476.2 x 476.7 mm
