ahmadmadyy/Coordinate-Tracking-Car/Hardware Design/DDOW Roller.SLDPRT

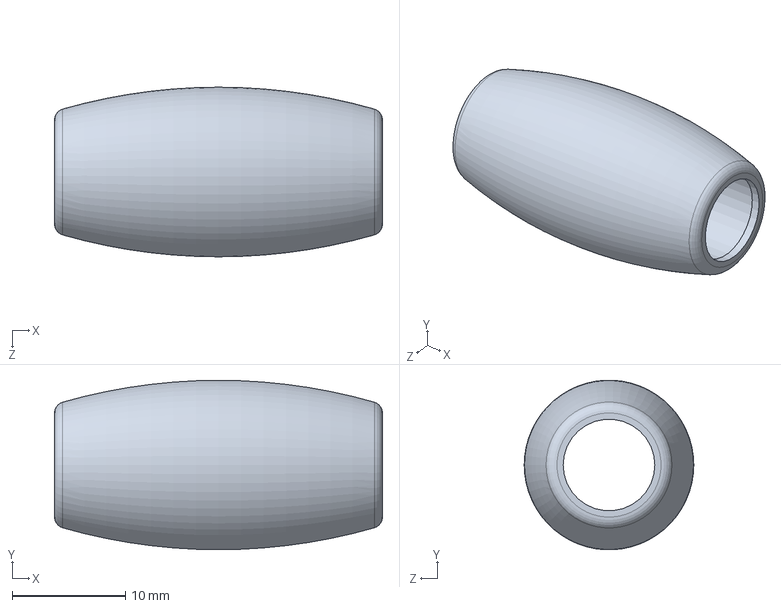
[picture p116: CAD file, 2023-09-04]
Hardware Design/DDOW Roller.SLDPRT
29.0 x 15.0 x 15.0 mm
