ahmadmadyy/Coordinate-Tracking-Car/Hardware Design/DDM Rotor.SLDPRT

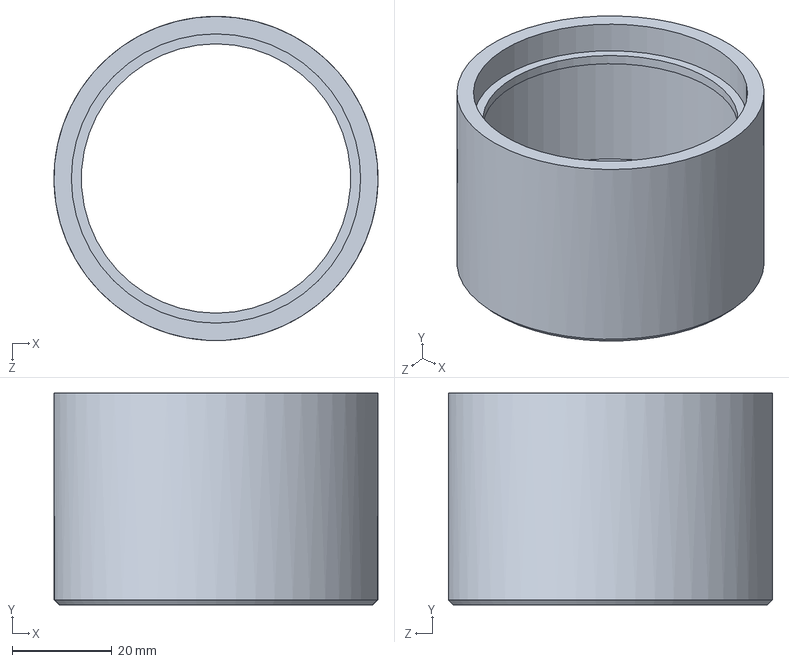
[picture p117: CAD file, 2023-09-04]
Hardware Design/DDM Rotor.SLDPRT
65.0 x 42.5 x 65.0 mm
