ahmadmadyy/Coordinate-Tracking-Car/Hardware Design/W 61809-2RS1.SLDPRT

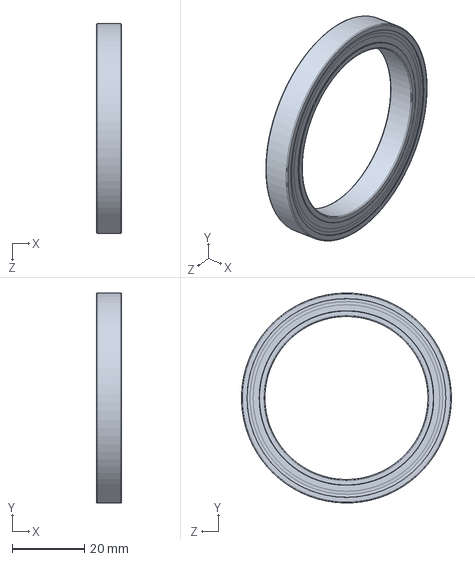
[picture p118: CAD file, 2023-09-04]
Hardware Design/W 61809-2RS1.SLDPRT
7.00 x 58.0 x 58.0 mm
