ahmadmadyy/Coordinate-Tracking-Car/Hardware Design/wheel.STEP

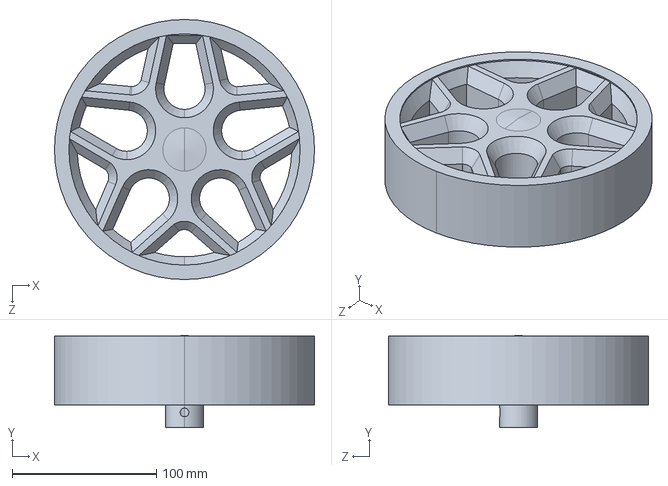
[picture p119: CAD file, 2023-09-04]
Hardware Design/wheel.STEP
180.0 x 63.8 x 180.0 mm
