ahmadmadyy/Coordinate-Tracking-Car/Hardware Design/DDOW Suport Shaft.SLDPRT

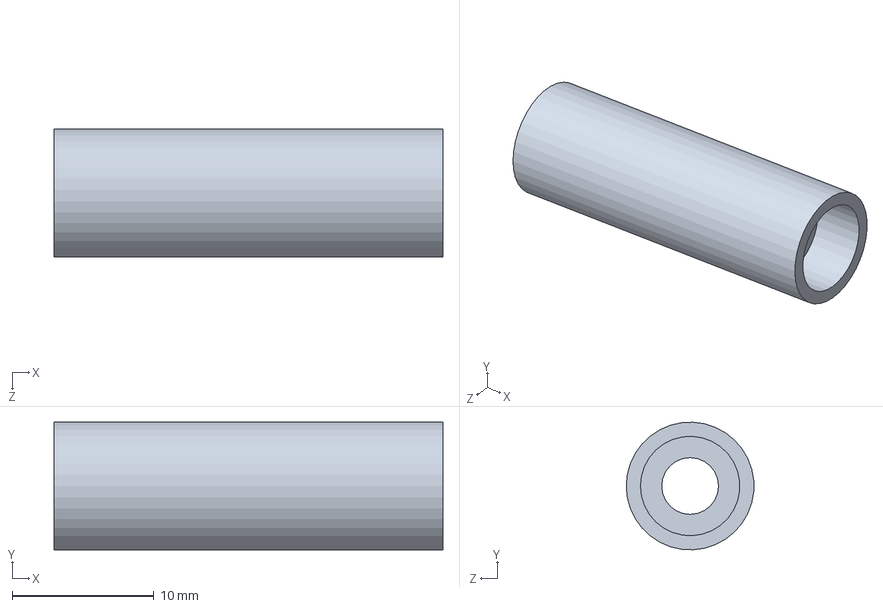
[picture p120: CAD file, 2023-09-04]
Hardware Design/DDOW Suport Shaft.SLDPRT
27.4 x 8.99 x 8.98 mm
