ahmadmadyy/Coordinate-Tracking-Car/Hardware Design/Castor wheel.STEP

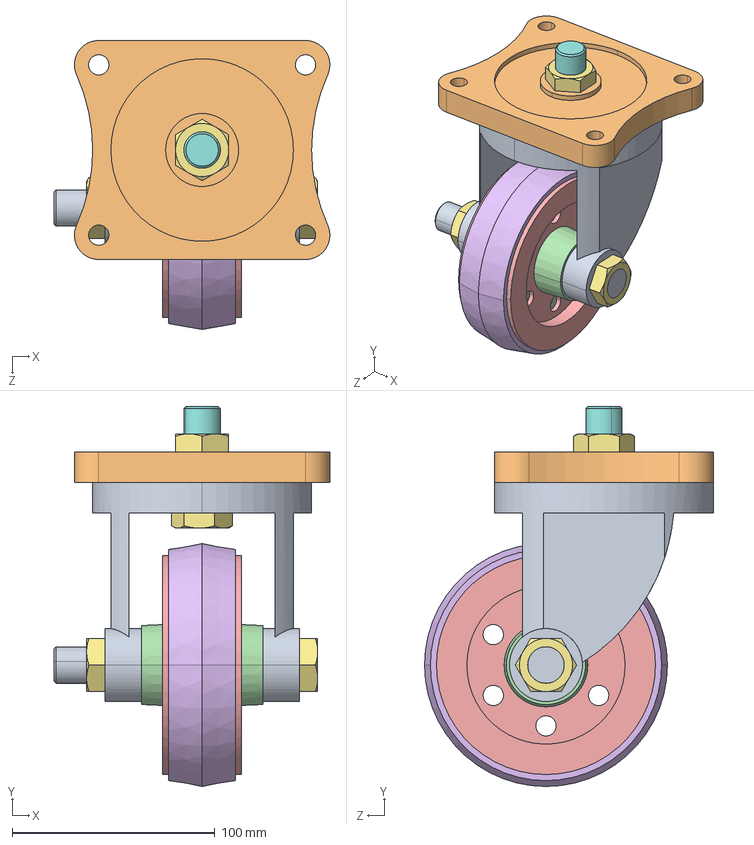
[picture p121: CAD file, 2023-09-04]
Hardware Design/Castor wheel.STEP
136.0 x 187.4 x 142.5 mm
Frame
Plate
Bush
Hub
Flange x 2
Tyre
Nut x 4
King-pin
Shaft
